GeunheePARKKK/Liquid_Control_Robot/docs/architecture/architecture.html

Dark

Style

Visual identityS cycles

ClassicStable technical default Signal FlowMotion-forward presentation BlueprintEngineering review EditorialPublication and launch notes

Live Present

Export

Export diagramPortable, clean outputs

E

Share Share Card1200×630 PNG Route Share Card1200×630 PNG Reach Share Card1200×630 PNG Copy Share CardPNG to clipboard Copy diagramPNG to clipboard

Image PNGLossless image JPEGCompact image WebPModern image

Vector & motion SVGEditable vector WebM6s motion

# Liquid Control Robot — 시스템 아키텍처

←

Guided views

Explore this system Step through curated paths without changing the source diagram.

Beat

→

▶ Play story # Copy moment Show all

Ready Chapter 01 / 01

Guided chapter

Diagram guide Explore this system ×

Inspecting compiled semantics

01 Find any nodeSearch labels, responsibilities, kinds, and stable IDs. / 02 Trace a routeAsk how two semantic nodes connect in authored direction. R 03 See the whole systemOpen Semantic Radar with a live viewport and stable nodes. M 04 Compare semantic kindsCount roles, reveal their traffic, and compare direct authored links. L 05 Play the guided storyWalk the authored chapters and real relationships. P 06 Enter Presentation StageGive the live diagram the viewport without changing export. F

E ExportT ThemeS Style0 Reset+ Zoom in- Zoom outEsc Close

Find a node ×

⌕ /

No matching nodes

Semantic passport

Verified source

Authored reach

Upstream0 Downstream0

× Copy link Relations

Route probe Choose a start node Find start Copy link Clear

Pick two semantic nodes on the diagram

← ▶ Journey → Overview

Choose the source, then the destination. Direction matters.

Semantic lens Compare system roles ×

Choose up to two semantic kinds. One reveals its real traffic; two compare only direct authored relationships.

Choose a kind to inspect its nodes and touching relationships.

Copy link Clear

Semantic radar Building overview Open radar ×

Click nodeDrag to pan

Semantic radar needs more MAP space.

PATH MAP LENS 100%

### 제어 법칙

- • 합력 벡터: θ_ref = atan(a_lin/g), 수평 유지와 가속 대응이 한 식
- • ZV 2 임펄스 입력성형, zf 실측 2.9 Hz (Ø8.9 cm, 400 mL)
- • 피드포워드 v_des + J·θ̈ (J = 0.0038), 모터 지연 70 → 25 ms
- • 지연 사슬 305 → 205 ms (LPF2 + FF, ZV 포함)

### 실측으로 밝힌 것

- • WiFi 켜면 CAN BUS_OFF → 와이파이판 보류, 유선으로 진행
- • DRV8825 Vref 1.6 V(3.2 A)가 과열·연기 원인, 0.4 V로 해결
- • 출발 충격 180 ms < 슬로싱 반주기 → 트레이가 한 박자 늦음
- • 센 사이클은 차체가 2.3~3.2 Hz로 흔들림, 서스펜션 강성 조절이 다음 실험

### 저장소

- • 루트 Liquid_Control_Robot.ino = zv_shaping_rtos + susTask
- • docs/CONTROL_INTEGRATION_TASK: 1~4단계 + 변경이력
- • gimbal_control / step_control / 주행부_모터 / servo_control
- • 보고서 그림·요구사항 정의서는 바탕화면 (SVG 먼저, PNG)
