GeunheePARKKK/Liquid_Control_Robot/hardware/CAD/new_robot/meshes/_____________.stl

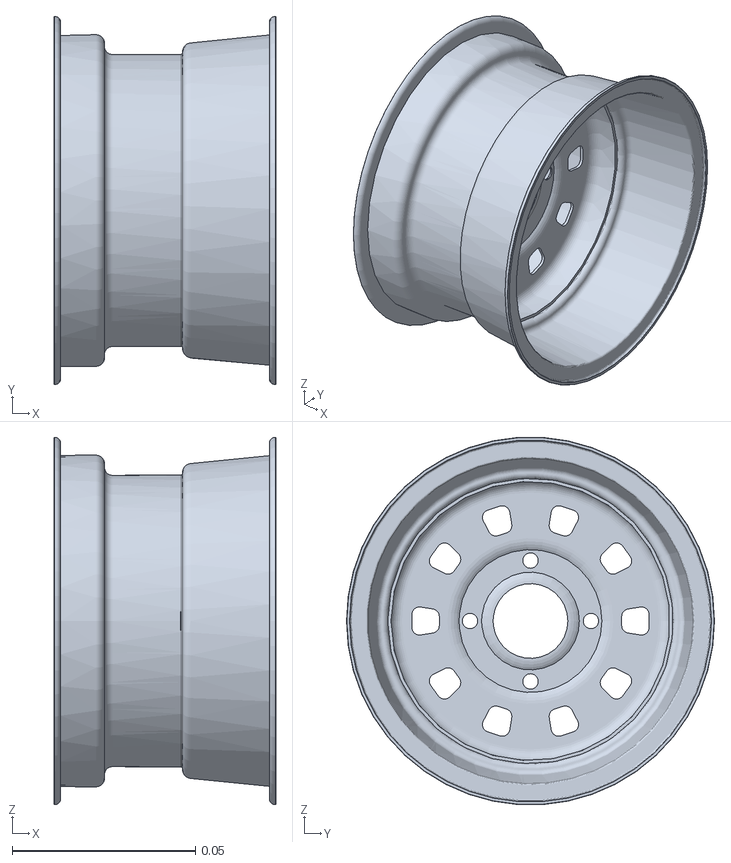
[picture p16: CAD file, 2026-08-16]
hardware/CAD/new_robot/meshes/_____________.stl
0.0606 x 0.101 x 0.1
