GeunheePARKKK/Liquid_Control_Robot/hardware/CAD/new_robot/meshes/Part_1.stl

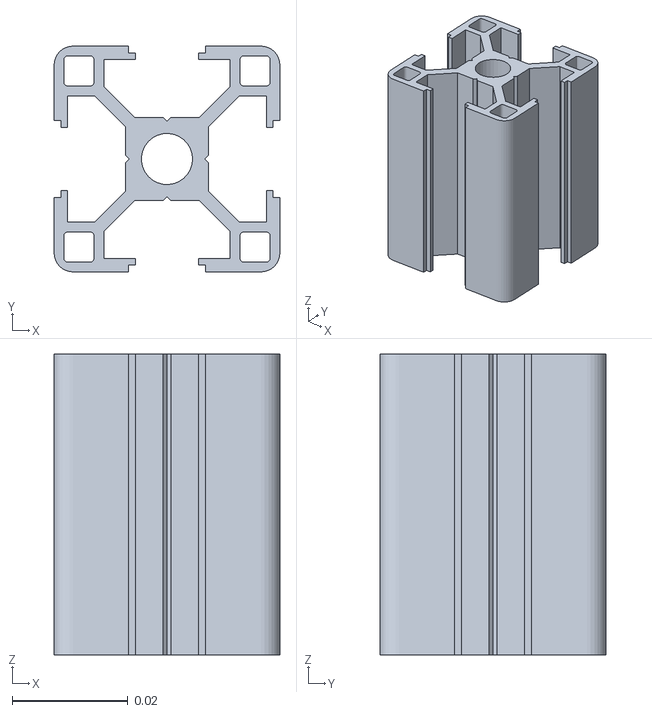
[picture p17: CAD file, 2026-08-16]
hardware/CAD/new_robot/meshes/Part_1.stl
0.039 x 0.039 x 0.052
