GeunheePARKKK/Liquid_Control_Robot/hardware/CAD/new_robot/meshes/GL60_V1_0_240806A_1_solid87.stl

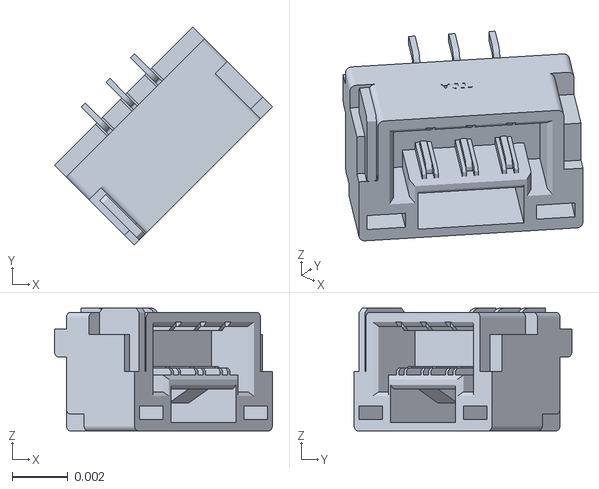
[picture p18: CAD file, 2026-08-16]
hardware/CAD/new_robot/meshes/GL60_V1_0_240806A_1_solid87.stl
0.00781 x 0.00781 x 0.0044
