GeunheePARKKK/Liquid_Control_Robot/hardware/CAD/new_robot/meshes/BJJ02040274_GL60II_______1_solid1.stl

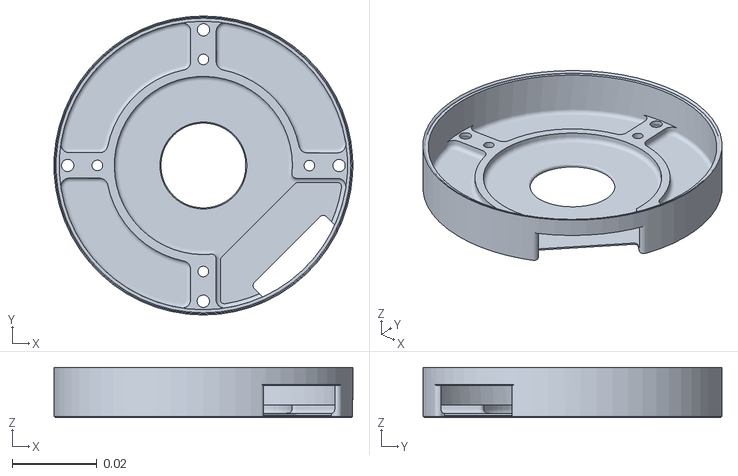
[picture p19: CAD file, 2026-08-16]
hardware/CAD/new_robot/meshes/BJJ02040274_GL60II_______1_solid1.stl
0.0704 x 0.0705 x 0.0118
